Seitanas/SeitanClock/display.h

void displayTime(configStructure *cfg, rtcData *tm, bool dot_state);
void displayTemperature(configStructure *cfg, rtcData *tm);
void displayYear(configStructure *cfg, rtcData *tm);
void displayMonthDay(configStructure *cfg, rtcData *tm);
void displayFlashMode(configStructure *cfg);
void displaySetupMode(configStructure *cfg);
void displayInit();
void brightness(int brightness);
